JMa-2/PortaNet/images/PXL_20220605_001210426.jpg

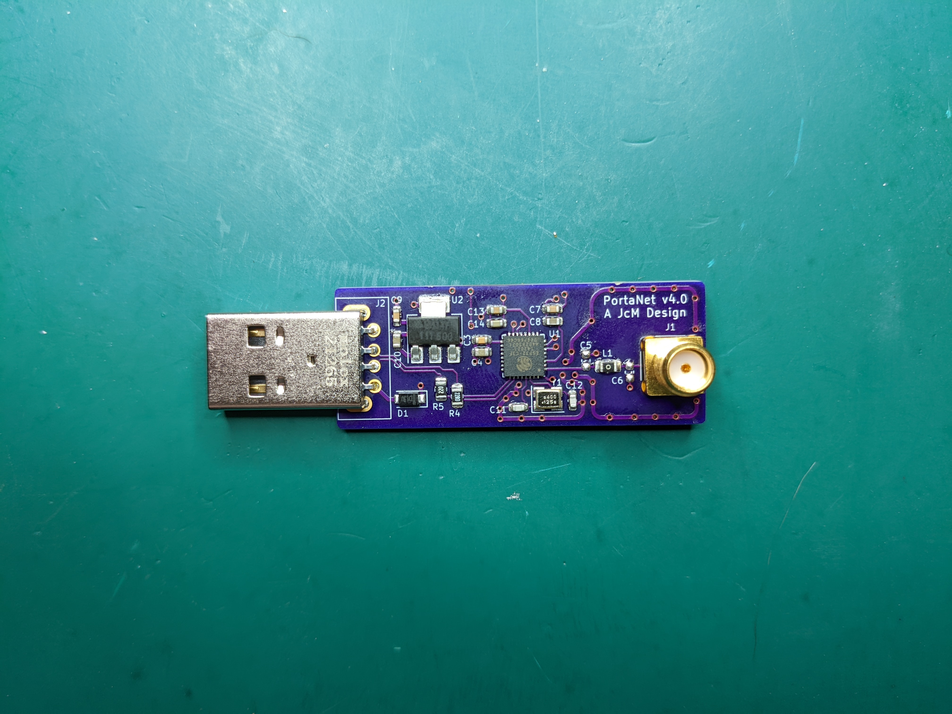
images/PXL_20220605_001210426.jpg
