JMa-2/PortaNet/images/PXL_20220605_001233367.jpg

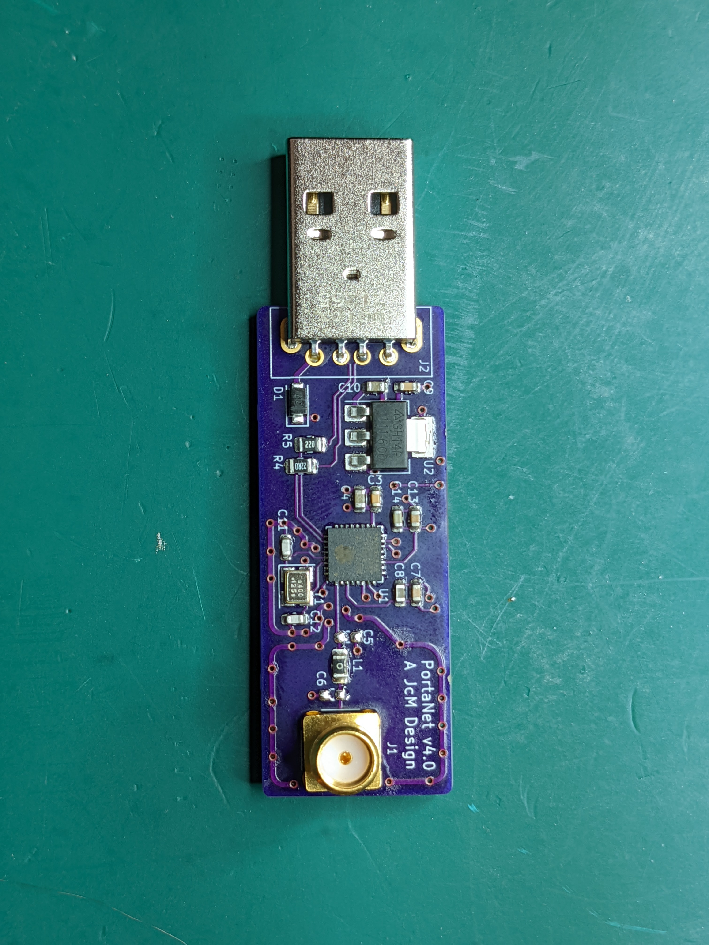
images/PXL_20220605_001233367.jpg
