JMa-2/PortaNet/images/PXL_20220605_001243593.jpg

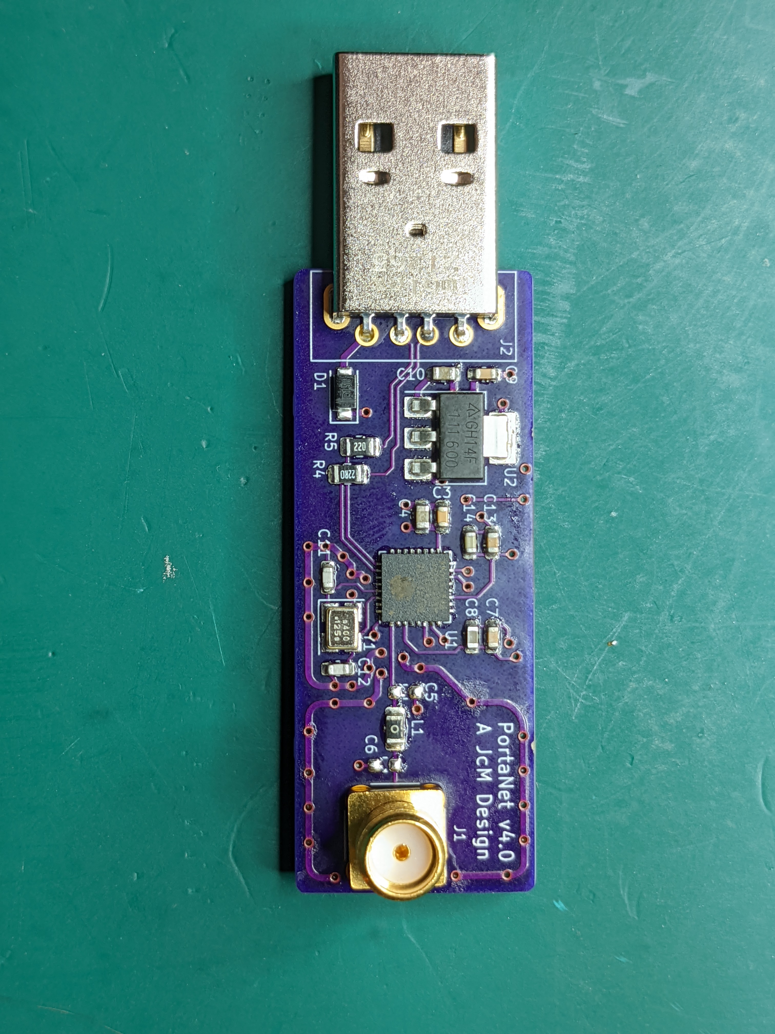
images/PXL_20220605_001243593.jpg
